rbgusrns/JP_Robotrace/Mechanics/STEP/SUCTION.STEP

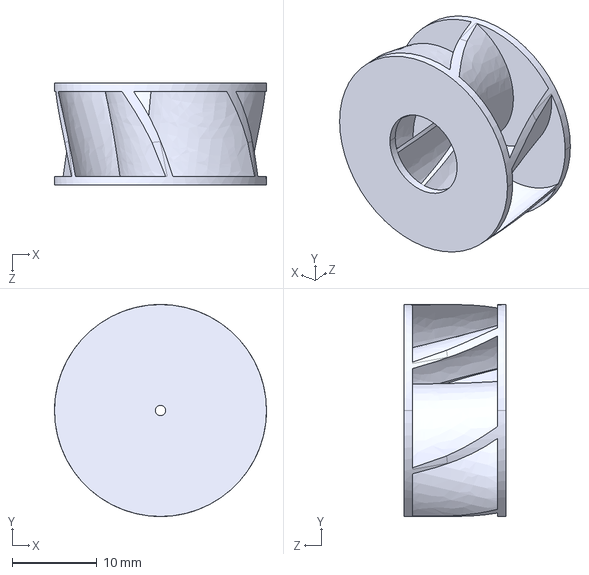
[picture p14: CAD file, 2026-03-30]
Mechanics/STEP/SUCTION.STEP
25.0 x 25.0 x 12.0 mm
