rbgusrns/JP_Robotrace/Software/main/fastrun.c

//###########################################################################
//
// FILE		: fastrun.c
//
// TITLE		: gungun_v2 Tracer fastrun source file.
//
// Author	: Park geon ju
//
// Company	: MAZE
//
//###########################################################################
// $Release Date: 2015.11.21 $
//###########################################################################


#include "DSP280x_Device.h"     // DSP280x Headerfile Include File
#include "DSP280x_Examples.h"   // DSP280x Examples Include File

static void turn_division_compute( fast_run_str *pinfo, int32 mark_cnt, error_str *perr ); 


// fast_error_compute( &g_err, pinfo, g_int32mark_cnt );	// 마크 에러처리  

void jerk_down( fast_run_str *pinfo, int32 mark_cnt )
{
	volatile _iq17 q17gone_dist = ( g_rm.q17gone_distance + g_lm.q17gone_distance ) >> 1;
	volatile _iq17 q17down_dist = _IQmpy(_IQ(pinfo->u16dist),_IQ(0.7));

	if( q17gone_dist > q17down_dist ) 
	{
		g_rm.int32accel = g_lm.int32accel = (int32)((g_q17user_acc>>17) + 2000 );
	}

}

void fast_error_compute( error_str *perr, fast_run_str *pinfo, int32 mark_cnt )
{
	fast_run_str *pnow;
	fast_run_str *pnext;

	volatile int32 dist = 0;
	volatile _iq17 big_vel = _IQ17(0.0);
	volatile _iq17 small_vel = _IQ17(0.0);

	perr->q17over_dist = ( g_rm.q17gone_distance + g_lm.q17gone_distance ) >> 1; // 현재 간 거리 계속 확인 	
	
	if( g_Flag.err )
	{
		g_Flag.fast_flag= OFF;
		return;
	}

	if( perr->q17over_dist > perr->q17err_dist[ mark_cnt ] ) // 마크에 주어진 에러값보다 더 간 경우 ( 마크를 놓친 경우) 
	{

		if(g_int32fasterror_flag)
		{
			if( g_int32err_cnt > 10 || mark_cnt > ( g_int32total_cnt - 1 ) ) // 1차 주행으로 전환 
			{
				VFDPrintf("   ERROR");

				g_Flag.err = ON;
				g_Flag.fast_flag= OFF;
			
				move_to_move(_IQ(1000), _IQ( 0 ), _IQ(1000) ,_IQ(1000), _IQ(5000));

				return;
			}
		}
		
		
		pnow = pinfo + mark_cnt;
		pnext = ( pinfo + mark_cnt + 1 );


		//	err_dst  - u16dist 
		dist = ( int32 )( (Uint16)(( perr->q17err_dist[ mark_cnt ] )>>17) - pnow->u16dist );

		pnext->u16dist -= dist;	// 실제 에러 수치를 다시 빼서 남은 거리를 구한다 . 
		if( pnext->u16dist <= 0 )
			pnext->u16dist = 10;

		//big_vel = ( pinfo->q17in_vel> pinfo->q17out_vel)? pinfo->q17in_vel : pinfo->q17out_vel;
		small_vel = ( pinfo->q17in_vel > pinfo->q17out_vel )? pinfo->q17out_vel : pinfo->q17in_vel;

		max_vel_compute( _IQ17( pnext->u16dist ), pnext->q17m_dist, small_vel, pnext->q17acc, &(pnext->q17vel) );	// 현재 거리와 등가속도에서 최고 속도를 계산 
		decel_dist_compute( pnext->q17vel, pnext->q17out_vel, pnext->q17acc, &(pnext->q17dec_dist) );			//  감속 거리 계산 

		perr->q17under_dist[ mark_cnt + 1 ] = _IQ17(( pnext->u16dist >> 1 ));

		second_infor( pinfo, perr);	// 마크를 강제로 처리한다.
		
	}

	
}


static void straight_compute( fast_run_str *pinfo, int32 mark_cnt, error_str *perr )  // straight, end compute
{ 
	volatile float32 big_vel = ( float32 )0.0;
	volatile float32 small_vel = ( float32 )0.0;


    
	pinfo->q17kp_val = POS_KP_UP;
	pinfo->s44s_flag = OFF;
	pinfo->speed_up_45 = OFF;

	//진입 속도, 탈출 속도 compute
	pinfo->q17in_vel = mark_cnt > 0 ? ( pinfo - 1 )->q17out_vel : _IQ17( 0.0);
    //첫 구간의 in_Vel = 0

	if( !( pinfo->u16turn_dir & ETURN ) )	//마지막 구간 아닐 경우. 일반적인 직진!
	{
		turn_division_compute( ( pinfo + 1 ), ( mark_cnt + 1 ), perr );	//다음 턴 미리 계산한 후에 out vel 결정
		pinfo->q17out_vel = ( pinfo + 1 )->q17in_vel;

		pinfo->q17out_vel = g_q17user_vel;			//턴속 모든 각에서 동일하게 맞춤 
	}
	else	//마지막 구간. ETURN
		( pinfo + 1 )->q17in_vel = pinfo->q17out_vel = g_q17end_vel;
		//( pinfo + 1 )->q17in_vel = pinfo->q17out_vel = _IQ17( 0.0);
		// 엔드마크의 in_Vel = 마지막 구간의 out_Vel = end_Vel
	//직진 길이별 가속도 설정
	
	if( pinfo->u16dist > LONG_DIST )        pinfo->q17acc = g_q17user_acc;
	else if( pinfo->u16dist> MID_DIST )		pinfo->q17acc = g_q17user_acc; //+ _IQ17(1000);  // 중간 직진 가속 
	else									pinfo->q17acc = g_q17user_acc;// + _IQ17(4000);

    if( pinfo->u16turn_dir & ETURN )        pinfo->q17acc = g_q17endturn_acc;

	if( !mark_cnt && pinfo->q17acc > _IQ17(10000) )	pinfo->q17acc = _IQ17(10000); // 시작 직전 가속도 제한

	big_vel = ( pinfo->q17in_vel> pinfo->q17out_vel)? pinfo->q17in_vel : pinfo->q17out_vel;
	small_vel = ( pinfo->q17in_vel > pinfo->q17out_vel )? pinfo->q17out_vel : pinfo->q17in_vel;
	
	decel_dist_compute( pinfo->q17in_vel, pinfo->q17out_vel, pinfo->q17acc, &pinfo->q17m_dist); // pinfo->q17m_dist 구함 
    //진입속도와 탈출속도, 가속도를 통해 감속 거리를 구함.
	if( pinfo->q17m_dist >=  _IQ17( ( pinfo->u16dist) ) ) // start or end
	{
		pinfo->q17dec_dist = _IQ17( ( pinfo->u16dist) );


		max_vel_compute( _IQ17( pinfo->u16dist ), _IQ17(0.0), small_vel, pinfo->q17acc , &pinfo->q17vel ); //pinfo->q17vel 구함 
		
		if( pinfo->q17in_vel > pinfo->q17out_vel )		pinfo->q17in_vel = pinfo->q17vel; // end
		else											pinfo->q17out_vel = pinfo->q17vel; // start 

		if( !mark_cnt )		//시작 직진
			pinfo->q17in_vel = _IQ17(0.0);
	}
	else
	{	
		max_vel_compute( _IQ17( pinfo->u16dist ), pinfo->q17m_dist, big_vel, pinfo->q17acc, &pinfo->q17vel );
		decel_dist_compute( pinfo->q17vel, pinfo->q17out_vel, pinfo->q17acc, &pinfo->q17dec_dist );
	}

	//에러 처리
	perr->q17err_dist[ mark_cnt ] = _IQ17( pinfo->u16dist << 2 );

	if( perr->q17err_dist[ mark_cnt ] > _IQ17( MID_DIST + SHORT_DIST ) )
		perr->q17err_dist[ mark_cnt ] = _IQ17( MID_DIST + SHORT_DIST );

	perr->q17err_dist[ mark_cnt ] += _IQ17( pinfo->u16dist );  // 곡률마다 에러값 지정. 마크를 못봤을 떄 필요 
	perr->q17under_dist[ mark_cnt ] = _IQmpy(_IQ17( pinfo->u16dist ) , _IQ17(0.9)); // 마크를 더 봤을 때 필요 

}


static void default_turn_compute( fast_run_str *pinfo, int32 mark_cnt, error_str *perr )
{
	pinfo->q17kp_val = POS_KP_UP;
	pinfo->s44s_flag = OFF;
	pinfo->speed_up_45 = OFF;

	pinfo->q17acc = g_q17user_acc;

	pinfo->q17in_vel = g_q17user_vel;
	pinfo->q17vel = pinfo->q17out_vel = pinfo->q17in_vel;

	//에러처리
	perr->q17err_dist[ mark_cnt ] = _IQmpy(_IQ17( pinfo->u16dist) ,_IQ17(0.5));
	perr->q17err_dist[ mark_cnt ] += _IQ17( pinfo->u16dist );

	perr->q17under_dist[ mark_cnt ] = _IQmpy(_IQ17( pinfo->u16dist) ,_IQ17(0.9));
	
	//45도 연속 

	if( ( pinfo->u16turn_dir & TURN_45 ) && ( ( pinfo + 1 )->u16turn_dir & ( TURN_45 | TURN_90 ) ) )
	{
		pinfo->speed_up_45 = ON;
		pinfo->q17kp_val = _IQ7(0.15);
		
		//에러처리
		perr->q17err_dist[ mark_cnt ] = _IQ17( pinfo->u16dist << 2 );
		perr->q17under_dist[ mark_cnt ] =_IQmpy(_IQ17( pinfo->u16dist) ,_IQ17(0.9));

        
	}


}

void large_turn_compute( fast_run_str *pinfo, int32 mark_cnt, error_str *perr )
{
	volatile _iq17 big_vel = _IQ17(0.0);
	volatile _iq17 small_vel = _IQ17(0.0);

	pinfo->q17kp_val = POS_KP_UP;
	pinfo->s44s_flag = OFF;
	pinfo->speed_up_45 = OFF;

	pinfo->q17in_vel = ( pinfo - 1 )->q17out_vel ? ( pinfo - 1 )->q17out_vel : g_q17user_vel;
	
	turn_division_compute( ( pinfo + 1 ), ( mark_cnt + 1 ), perr ); // 다음 턴 미리 계산한 후에 out_vel 결정 
	pinfo->q17out_vel = ( pinfo + 1 )->q17in_vel;

	

	if( pinfo->q17out_vel == _IQ17(0.0))				pinfo->q17out_vel = ( g_q17user_vel);
	if( pinfo->q17in_vel > ( g_q17large_vel) )			pinfo->q17in_vel = ( g_q17large_vel );
	if( pinfo->q17out_vel > ( g_q17large_vel ) )		pinfo->q17out_vel = ( g_q17large_vel );
	pinfo->q17acc = g_q17large_acc;


	big_vel = ( pinfo->q17in_vel> pinfo->q17out_vel)? pinfo->q17in_vel : pinfo->q17out_vel;
	small_vel = ( pinfo->q17in_vel > pinfo->q17out_vel )? pinfo->q17out_vel : pinfo->q17in_vel;
	decel_dist_compute( pinfo->q17in_vel, pinfo->q17out_vel, pinfo->q17acc, &pinfo->q17m_dist );

	if( pinfo->q17m_dist >=  _IQ17( ( pinfo->u16dist) ) )
	{
		pinfo->q17dec_dist = _IQ17( ( pinfo->u16dist) );
		max_vel_compute( _IQ17( pinfo->u16dist ), _IQ17(0.0), small_vel, pinfo->q17acc , &pinfo->q17vel );

		if( pinfo->q17in_vel > pinfo->q17out_vel )		pinfo->q17in_vel = pinfo->q17vel;
		else											pinfo->q17out_vel = pinfo->q17vel;

		if( !mark_cnt )		//시작 직진
			pinfo->q17in_vel = _IQ17(0.0);
	}
	else
	{
		
		
		max_vel_compute( _IQ17( pinfo->u16dist ), pinfo->q17m_dist, big_vel, pinfo->q17acc, &pinfo->q17vel );
		decel_dist_compute( pinfo->q17vel, pinfo->q17out_vel, pinfo->q17acc, &pinfo->q17dec_dist );

		//if( ((pinfo + 1)->u16turn_way & STRAIGHT) && ( (pinfo + 1)->u16dist > SHORT_DIST) ) ( pinfo + 1 )->q17in_vel = pinfo->q17out_vel = pinfo->q17vel;		// 다음턴이 직진인 경우 q17vel로 탈출  // 큰턴 + 직진 가속 
	}


	//에러 처리
	perr->q17err_dist[ mark_cnt ] = _IQ17( pinfo->u16dist << 2 );
	if( perr->q17err_dist[ mark_cnt ] > _IQ17( MID_DIST + SHORT_DIST ) )
		perr->q17err_dist[ mark_cnt ] = _IQ17( MID_DIST + SHORT_DIST );

	perr->q17err_dist[ mark_cnt ] += _IQ17( pinfo->u16dist );
	perr->q17under_dist[ mark_cnt ] = _IQmpy(_IQ17( pinfo->u16dist ) , _IQ17(0.9));

}


static void turn_division_compute( fast_run_str *pinfo, int32 mark_cnt, error_str *perr ) // 직진, 큰턴, 턴 구분 
{
    TxPrintf("way: %d\n",pinfo->u16turn_dir);
	if( pinfo->u16turn_way & (STRAIGHT | ETURN ) )			                            straight_compute( pinfo, mark_cnt, perr );
	else if( pinfo->u16turn_dir & LARGE_TURN )											default_turn_compute( pinfo, mark_cnt, perr ); //large_turn_compute( pinfo, mark_cnt, perr );
	else																				default_turn_compute( pinfo, mark_cnt, perr );
}

void turn_division_func( void )
{
		int32 i = 0;
		TxPrintf("cnt: %ld\n",g_int32total_cnt);
		for( i = 0; i < g_int32total_cnt; i++ )
		{
			/*
			if( 1 == ( g_int32total_cnt - 1 ) )
			{
				if( g_fast_info[ i ].q17acc>= _IQ17(12000) )
					g_fast_info[ i ].q17acc = _IQ17(12000);
					g_q17end_acc = g_fast_info[ i ].q17acc;

			}
			*/

			turn_division_compute( &g_fast_info[ i ], i, &g_err );

			
		}
	
	
}


void speed_up_compute( fast_run_str *p_info )
{
	fast_run_str *pinfo = p_info;

	
	if( !g_Flag.speed_up_start || g_Flag.err )	return;
#if 0
	g_int32speed_up_cnt ++;
	if( g_int32speed_up_cnt > ( pinfo + g_int32mark_cnt - 1 )->u16turn_cnt  || !( g_int32mark_cnt ) )
	{
        
		g_Flag.speed_up = ON;
		g_Flag.speed_up_start = OFF;
		g_int32speed_up_cnt = 0;
	}
#endif

#if 1
	if( g_q17straight_dist >= ( _IQ(( pinfo + g_int32mark_cnt - 1 )->u16turn_cnt) )  || !( g_int32mark_cnt ) )
	{
		g_Flag.speed_up = ON;
		g_Flag.speed_up_start = OFF;
		g_int32speed_up_cnt = 0;
	}
#endif


}


void second_infor(fast_run_str * p_info, error_str *perr )
{

	fast_run_str *pinfo = p_info;

	// 턴마크 나올 거리가 안됐을 경우(마크를 더 찍은 경우) 
	if( g_Flag.err || ( perr->q17over_dist < perr->q17under_dist[ g_int32mark_cnt ] ) )	
    {
        return;
    }
    
    //if( ( ( pinfo + g_int32mark_cnt + 1 )->u16turn_dir & ( STRAIGHT | ETURN ) ) && !( g_pos.u16current_state & STRAIGHT ) )
    //{
    //    return;
    //}    

    //if( !( ( pinfo + g_int32mark_cnt + 1 )->u16turn_way & g_pos.u16current_state ) )
    //{
    //    return;
    //}
	g_int32mark_cnt ++; // 저장된 곡률보다 한칸 뒷 정보를 불러와야 함. 


	if( g_Flag.err == OFF )
	{

		if( ( g_int32total_cnt + 5 ) < g_int32mark_cnt )
		{
			g_Flag.err = ON;
			g_lm.q17gone_distance = g_rm.q17gone_distance = _IQ17(0.0); // 검출용 변수들 다시 초기화 
			return;
		}
	}

	if( ( pinfo + g_int32mark_cnt )->u16turn_dir & ( STRAIGHT | LARGE_TURN | ETURN ) )
    {
            g_Flag.speed_up_start = ON;  // 가속 시작 flag on
            g_lmark.u16mark_enable = FRONT_MARK_CHECK;
            
	}
    else if( ( pinfo + g_int32mark_cnt )->q17kp_val == POS_KP_DOWN )
    {
            g_lmark.u16mark_enable = ( FRONT_MARK_CHECK | LEFT_MARK_CHECK );
    }
	else																					
    {
        g_Flag.straight_run = OFF;
        g_lmark.u16mark_enable = LEFT_MARK_CHECK;
	}


	move_to_move( _IQ17( ( pinfo + g_int32mark_cnt )->u16dist ), ( pinfo + g_int32mark_cnt )->q17dec_dist, ( pinfo + g_int32mark_cnt )->q17vel, ( pinfo + g_int32mark_cnt )->q17out_vel, ( pinfo + g_int32mark_cnt )->q17acc );
    
	perr->q17over_dist = _IQ17( 0.0 );
	g_lm.q17gone_distance = g_rm.q17gone_distance = _IQ17(0.0); // 검출용 변수들 다시 초기화 
	g_lm.q17total_dist = g_rm.q17total_dist = _IQ(0.0);
    g_rm.q17dist_sum = g_lm.q17dist_sum = _IQ(0.0);
 
	g_pos.u16past_state = ( pinfo + g_int32mark_cnt )->u16turn_dir;	
    
}

   
void print_sec_info(fast_run_str *pinfo)
{
	race_start_init();
	//fast_infor_read_rom(); 
	turn_info_func();
	turn_division_func();

	//g_fast_info[g_int32total_cnt-1].q17out_vel = _IQ(2400);	// 마지막 탈출속도 고정
	print_second_info();
}

void second_run(fast_run_str *pinfo)
{	
	
	//int32 i = 0;
	
	race_start_init();
	//fast_infor_read_rom(); 
	turn_info_func();
	turn_division_func();
    //print_second_info();
	
	VFDPrintf("fst %f",_IQ17toF(g_q17user_vel));	

    DELAY_US(500000);

    FAN_ON;
    
	DELAY_US(1000000);
    
	VFDPrintf("        ");

	
	// 1차 handle : 0.52 1.88 / 
	handle_ad_make(g_q16out_corner_fast_limit, g_q16in_corner_fast_limit); // _IQ16(0.35) , _IQ16(2.05);
	move_to_move( _IQ17( pinfo->u16dist ), pinfo->q17dec_dist, pinfo->q17vel, pinfo->q17out_vel, pinfo->q17acc );
    //TxPrintf("%d,%ld,%ld,%ld,%ld\n",pinfo->u16dist, pinfo->q17dec_dist >> 17 , pinfo->q17vel >> 17 , pinfo->q17out_vel >> 17 , pinfo->q17acc >> 17 );
	g_Flag.fast_flag = ON;
	g_Flag.motor_start = ON;
	
	while(1)
	{
        //TxPrintf("%f,%f,%f,%f,%ld,%d,%d,%ld\n",_IQtoF(g_q17current_omega),_IQtoF(g_err.q17err_dist[ g_int32mark_cnt ]),_IQtoF(g_err.q17under_dist[ g_int32mark_cnt ]),_IQtoF(g_err.q17over_dist),g_int32mark_cnt,g_pos.u16past_state<<6,g_pos.u16current_state<<6,g_int32err_cnt );
         //TxPrintf("%f,%ld\n",_IQtoF(g_q17current_omega),g_int32mark_cnt);
        //TxPrintf("%f,%f,%ld,%u,%u\n",_IQtoF(g_q17current_omega),_IQtoF(g_err.q17over_dist),g_int32mark_cnt,g_pos.u16current_state<<6,(pinfo+g_int32mark_cnt)->u16turn_way<<6);
        //LED_ON;
        g_q17straight_dist = (g_rm.q17gone_distance + g_lm.q17gone_distance) >> 1 ;
	
		make_position();
		
		if(g_Flag.move_state)
		{
			g_lmark.q7turn_dis = (g_lmark.q7check_dis + g_rmark.q7check_dis) >> 1;
			g_rmark.q7turn_dis = g_lmark.q7turn_dis;
	
			turn_decide( g_ptr->g_lmark );
			turn_decide( g_ptr->g_rmark );
			
			
		}

						
		if( g_Flag.motor_ISR_flag )
		{
			if( lineout_func())
			{
                g_Flag.motor_ISR_flag = OFF;
				return;
			}

			speed_up_compute( pinfo );
            fast_error_compute( &g_err, pinfo, g_int32mark_cnt );		        
			g_Flag.motor_ISR_flag = OFF;
		}	
        //LED_OFF;
	}
}
