rbgusrns/JP_Robotrace/Software/include/IQmathLib.h

//###########################################################################
//
// FILE:	IQmathLib.h
//
// TITLE:	IQ Math library functions definitions.
//
//###########################################################################
//
// Ver  | dd-mmm-yyyy |  Who  | Description of changes
// =====|=============|=======|==============================================
//  1.3 | 19 Nov 2001 | A. T. | Original Release.
// -----|-------------|-------|----------------------------------------------
//  1.4 | 17 May 2002 | A. T. | Added new functions and support for
//      |             |       | intrinsics IQmpy, IQxmpy, IQsat.
// -----|-------------|-------|----------------------------------------------
//  1.4a| 12 Jun 2002 | A. T. | Fixed problem with _IQ() operation on
//      |             |       | variables.
// -----|-------------|-------|----------------------------------------------
//  1.4b| 18 Jun 2002 | A. T. | Fixed bug with _IQtoIQN() and _IQNtoIQ()
//      |             |       | operations.
// -----|-------------|-------|----------------------------------------------
//  1.4d| 30 Mar 2003 | DA/SD | 1. Added macro parameters in parentheses 
//      |             |       |    in number of places where it matters
//      |             |       | 2. Added macro definition to include header 
//      |             |       |    file multiple times in the program.     
// -----|-------------|-------|----------------------------------------------
//
//###########################################################################
// 
// User needs to configure "MATH_TYPE" and "GLOBAL_Q" values:
//
//---------------------------------------------------------------------------
// Select math type, IQ_MATH or FLOAT_MATH:
//

#ifndef __IQMATHLIB_H_INCLUDED__
#define __IQMATHLIB_H_INCLUDED__


#define   FLOAT_MATH     1
#define   IQ_MATH        0

#ifndef   MATH_TYPE
#define   MATH_TYPE      IQ_MATH
#endif

//---------------------------------------------------------------------------
// Select global Q value and scaling. The Q value is limited to the 
// following range for all functions:
//
//        30 <= GLOBAL_Q <=  1
//
#ifndef   GLOBAL_Q
#define   GLOBAL_Q       17
#endif

//---------------------------------------------------------------------------
// Various Usefull Constant Definitions:
//
#define   QG          GLOBAL_Q
#define   Q30         30
#define   Q29         29
#define   Q28         28
#define   Q27         27
#define   Q26         26
#define   Q25         25
#define   Q24         24
#define   Q23         23
#define   Q22         22
#define   Q21         21
#define   Q20         20
#define   Q19         19
#define   Q18         18
#define   Q17         17
#define   Q16         16
#define   Q15         15
#define   Q14         14
#define   Q13         13
#define   Q12         12
#define   Q11         11
#define   Q10         10
#define   Q9          9
#define   Q8          8
#define   Q7          7
#define   Q6          6
#define   Q5          5
#define   Q4          4
#define   Q3          3
#define   Q2          2
#define   Q1          1

#define   MAX_IQ_POS  2147483647 
#define   MAX_IQ_NEG  -2147483648
#define   MIN_IQ_POS  1
#define   MIN_IQ_NEG  -1

//###########################################################################
#if MATH_TYPE == IQ_MATH
//###########################################################################
// If IQ_MATH is used, the following IQmath library function definitions
// are used:
//===========================================================================
typedef   long    _iq;
typedef   long    _iq30;
typedef   long    _iq29;
typedef   long    _iq28;
typedef   long    _iq27;
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

#define   _IQtoIQ28(A)  ((GLOBAL_Q >= 28) ? ((long) (A) >> (GLOBAL_Q - 28)):((long) (A) << (28 - GLOBAL_Q)))
#define   _IQ28toIQ(A)  ((GLOBAL_Q >= 28) ? ((long) (A) << (GLOBAL_Q - 28)):((long) (A) >> (28 - GLOBAL_Q)))

#define   _IQtoIQ27(A)  ((GLOBAL_Q >= 27) ? ((long) (A) >> (GLOBAL_Q - 27)):((long) (A) << (27 - GLOBAL_Q)))
#define   _IQ27toIQ(A)  ((GLOBAL_Q >= 27) ? ((long) (A) << (GLOBAL_Q - 27)):((long) (A) >> (27 - GLOBAL_Q)))

#define   _IQtoIQ26(A)  ((GLOBAL_Q >= 26) ? ((long) (A) >> (GLOBAL_Q - 26)):((long) (A) << (26 - GLOBAL_Q)))
#define   _IQ26toIQ(A)  ((GLOBAL_Q >= 26) ? ((long) (A) << (GLOBAL_Q - 26)):((long) (A) >> (26 - GLOBAL_Q)))

#define   _IQtoIQ25(A)  ((GLOBAL_Q >= 25) ? ((long) (A) >> (GLOBAL_Q - 25)):((long) (A) << (25 - GLOBAL_Q)))
#define   _IQ25toIQ(A)  ((GLOBAL_Q >= 25) ? ((long) (A) << (GLOBAL_Q - 25)):((long) (A) >> (25 - GLOBAL_Q)))

#define   _IQtoIQ24(A)  ((GLOBAL_Q >= 24) ? ((long) (A) >> (GLOBAL_Q - 24)):((long) (A) << (24 - GLOBAL_Q)))
#define   _IQ24toIQ(A)  ((GLOBAL_Q >= 24) ? ((long) (A) << (GLOBAL_Q - 24)):((long) (A) >> (24 - GLOBAL_Q)))

#define   _IQtoIQ23(A)  ((GLOBAL_Q >= 23) ? ((long) (A) >> (GLOBAL_Q - 23)):((long) (A) << (23 - GLOBAL_Q)))
#define   _IQ23toIQ(A)  ((GLOBAL_Q >= 23) ? ((long) (A) << (GLOBAL_Q - 23)):((long) (A) >> (23 - GLOBAL_Q)))

#define   _IQtoIQ22(A)  ((GLOBAL_Q >= 22) ? ((long) (A) >> (GLOBAL_Q - 22)):((long) (A) << (22 - GLOBAL_Q)))
#define   _IQ22toIQ(A)  ((GLOBAL_Q >= 22) ? ((long) (A) << (GLOBAL_Q - 22)):((long) (A) >> (22 - GLOBAL_Q)))

#define   _IQtoIQ21(A)  ((GLOBAL_Q >= 21) ? ((long) (A) >> (GLOBAL_Q - 21)):((long) (A) << (21 - GLOBAL_Q)))
#define   _IQ21toIQ(A)  ((GLOBAL_Q >= 21) ? ((long) (A) << (GLOBAL_Q - 21)):((long) (A) >> (21 - GLOBAL_Q)))

#define   _IQtoIQ20(A)  ((GLOBAL_Q >= 20) ? ((long) (A) >> (GLOBAL_Q - 20)):((long) (A) << (20 - GLOBAL_Q)))
#define   _IQ20toIQ(A)  ((GLOBAL_Q >= 20) ? ((long) (A) << (GLOBAL_Q - 20)):((long) (A) >> (20 - GLOBAL_Q)))

#define   _IQtoIQ19(A)  ((GLOBAL_Q >= 19) ? ((long) (A) >> (GLOBAL_Q - 19)):((long) (A) << (19 - GLOBAL_Q)))
#define   _IQ19toIQ(A)  ((GLOBAL_Q >= 19) ? ((long) (A) << (GLOBAL_Q - 19)):((long) (A) >> (19 - GLOBAL_Q)))

#define   _IQtoIQ18(A)  ((GLOBAL_Q >= 18) ? ((long) (A) >> (GLOBAL_Q - 18)):((long) (A) << (18 - GLOBAL_Q)))
#define   _IQ18toIQ(A)  ((GLOBAL_Q >= 18) ? ((long) (A) << (GLOBAL_Q - 18)):((long) (A) >> (18 - GLOBAL_Q)))

#define   _IQtoIQ17(A)  ((GLOBAL_Q >= 17) ? ((long) (A) >> (GLOBAL_Q - 17)):((long) (A) << (17 - GLOBAL_Q)))
#define   _IQ17toIQ(A)  ((GLOBAL_Q >= 17) ? ((long) (A) << (GLOBAL_Q - 17)):((long) (A) >> (17 - GLOBAL_Q)))

#define   _IQtoIQ16(A)  ((GLOBAL_Q >= 16) ? ((long) (A) >> (GLOBAL_Q - 16)):((long) (A) << (16 - GLOBAL_Q)))
#define   _IQ16toIQ(A)  ((GLOBAL_Q >= 16) ? ((long) (A) << (GLOBAL_Q - 16)):((long) (A) >> (16 - GLOBAL_Q)))

#define   _IQtoIQ15(A)  ((GLOBAL_Q >= 15) ? ((long) (A) >> (GLOBAL_Q - 15)):((long) (A) << (15 - GLOBAL_Q)))
#define   _IQ15toIQ(A)  ((GLOBAL_Q >= 15) ? ((long) (A) << (GLOBAL_Q - 15)):((long) (A) >> (15 - GLOBAL_Q)))

#define   _IQtoIQ14(A)  ((GLOBAL_Q >= 14) ? ((long) (A) >> (GLOBAL_Q - 14)):((long) (A) << (14 - GLOBAL_Q)))
#define   _IQ14toIQ(A)  ((GLOBAL_Q >= 14) ? ((long) (A) << (GLOBAL_Q - 14)):((long) (A) >> (14 - GLOBAL_Q)))

#define   _IQtoIQ13(A)  ((GLOBAL_Q >= 13) ? ((long) (A) >> (GLOBAL_Q - 13)):((long) (A) << (13 - GLOBAL_Q)))
#define   _IQ13toIQ(A)  ((GLOBAL_Q >= 13) ? ((long) (A) << (GLOBAL_Q - 13)):((long) (A) >> (13 - GLOBAL_Q)))

#define   _IQtoIQ12(A)  ((GLOBAL_Q >= 12) ? ((long) (A) >> (GLOBAL_Q - 12)):((long) (A) << (12 - GLOBAL_Q)))
#define   _IQ12toIQ(A)  ((GLOBAL_Q >= 12) ? ((long) (A) << (GLOBAL_Q - 12)):((long) (A) >> (12 - GLOBAL_Q)))

#define   _IQtoIQ11(A)  ((GLOBAL_Q >= 11) ? ((long) (A) >> (GLOBAL_Q - 11)):((long) (A) << (11 - GLOBAL_Q)))
#define   _IQ11toIQ(A)  ((GLOBAL_Q >= 11) ? ((long) (A) << (GLOBAL_Q - 11)):((long) (A) >> (11 - GLOBAL_Q)))

#define   _IQtoIQ10(A)  ((GLOBAL_Q >= 10) ? ((long) (A) >> (GLOBAL_Q - 10)):((long) (A) << (10 - GLOBAL_Q)))
#define   _IQ10toIQ(A)  ((GLOBAL_Q >= 10) ? ((long) (A) << (GLOBAL_Q - 10)):((long) (A) >> (10 - GLOBAL_Q)))

#define   _IQtoIQ9(A)   ((GLOBAL_Q >= 9) ? ((long) (A) >> (GLOBAL_Q - 9)):((long) (A) << (9 - GLOBAL_Q)))
#define   _IQ9toIQ(A)   ((GLOBAL_Q >= 9) ? ((long) (A) << (GLOBAL_Q - 9)):((long) (A) >> (9 - GLOBAL_Q)))

#define   _IQtoIQ8(A)   ((GLOBAL_Q >= 8) ? ((long) (A) >> (GLOBAL_Q - 8)):((long) (A) << (8 - GLOBAL_Q)))
#define   _IQ8toIQ(A)   ((GLOBAL_Q >= 8) ? ((long) (A) << (GLOBAL_Q - 8)):((long) (A) >> (8 - GLOBAL_Q)))

#define   _IQtoIQ7(A)   ((GLOBAL_Q >= 7) ? ((long) (A) >> (GLOBAL_Q - 7)):((long) (A) << (7 - GLOBAL_Q)))
#define   _IQ7toIQ(A)   ((GLOBAL_Q >= 7) ? ((long) (A) << (GLOBAL_Q - 7)):((long) (A) >> (7 - GLOBAL_Q)))

#define   _IQtoIQ6(A)   ((GLOBAL_Q >= 6) ? ((long) (A) >> (GLOBAL_Q - 6)):((long) (A) << (6 - GLOBAL_Q)))
#define   _IQ6toIQ(A)   ((GLOBAL_Q >= 6) ? ((long) (A) << (GLOBAL_Q - 6)):((long) (A) >> (6 - GLOBAL_Q)))

#define   _IQtoIQ5(A)   ((GLOBAL_Q >= 5) ? ((long) (A) >> (GLOBAL_Q - 5)):((long) (A) << (5 - GLOBAL_Q)))
#define   _IQ5toIQ(A)   ((GLOBAL_Q >= 5) ? ((long) (A) << (GLOBAL_Q - 5)):((long) (A) >> (5 - GLOBAL_Q)))

#define   _IQtoIQ4(A)   ((GLOBAL_Q >= 4) ? ((long) (A) >> (GLOBAL_Q - 4)):((long) (A) << (4 - GLOBAL_Q)))
#define   _IQ4toIQ(A)   ((GLOBAL_Q >= 4) ? ((long) (A) << (GLOBAL_Q - 4)):((long) (A) >> (4 - GLOBAL_Q)))

#define   _IQtoIQ3(A)   ((GLOBAL_Q >= 3) ? ((long) (A) >> (GLOBAL_Q - 3)):((long) (A) << (3 - GLOBAL_Q)))
#define   _IQ3toIQ(A)   ((GLOBAL_Q >= 3) ? ((long) (A) << (GLOBAL_Q - 3)):((long) (A) >> (3 - GLOBAL_Q)))

#define   _IQtoIQ2(A)   ((GLOBAL_Q >= 2) ? ((long) (A) >> (GLOBAL_Q - 2)):((long) (A) << (2 - GLOBAL_Q)))
#define   _IQ2toIQ(A)   ((GLOBAL_Q >= 2) ? ((long) (A) << (GLOBAL_Q - 2)):((long) (A) >> (2 - GLOBAL_Q)))

#define   _IQtoIQ1(A)   ((long) (A) >> (GLOBAL_Q - 1))
#define   _IQ1toIQ(A)   ((long) (A) << (GLOBAL_Q - 1))
//---------------------------------------------------------------------------
#define   _IQtoQ15(A)   ((GLOBAL_Q >= 15) ? ((long) (A) >> (GLOBAL_Q - 15)):((long) (A) << (15 - GLOBAL_Q)))
#define   _Q15toIQ(A)   ((GLOBAL_Q >= 15) ? ((long) (A) << (GLOBAL_Q - 15)):((long) (A) >> (15 - GLOBAL_Q)))

#define   _IQtoQ14(A)   ((GLOBAL_Q >= 14) ? ((long) (A) >> (GLOBAL_Q - 14)):((long) (A) << (14 - GLOBAL_Q)))
#define   _Q14toIQ(A)   ((GLOBAL_Q >= 14) ? ((long) (A) << (GLOBAL_Q - 14)):((long) (A) >> (14 - GLOBAL_Q)))

#define   _IQtoQ13(A)   ((GLOBAL_Q >= 13) ? ((long) (A) >> (GLOBAL_Q - 13)):((long) (A) << (13 - GLOBAL_Q)))
#define   _Q13toIQ(A)   ((GLOBAL_Q >= 13) ? ((long) (A) << (GLOBAL_Q - 13)):((long) (A) >> (13 - GLOBAL_Q)))

#define   _IQtoQ12(A)   ((GLOBAL_Q >= 12) ? ((long) (A) >> (GLOBAL_Q - 12)):((long) (A) << (12 - GLOBAL_Q)))
#define   _Q12toIQ(A)   ((GLOBAL_Q >= 12) ? ((long) (A) << (GLOBAL_Q - 12)):((long) (A) >> (12 - GLOBAL_Q)))

#define   _IQtoQ11(A)   ((GLOBAL_Q >= 11) ? ((long) (A) >> (GLOBAL_Q - 11)):((long) (A) << (11 - GLOBAL_Q)))
#define   _Q11toIQ(A)   ((GLOBAL_Q >= 11) ? ((long) (A) << (GLOBAL_Q - 11)):((long) (A) >> (11 - GLOBAL_Q)))

#define   _IQtoQ10(A)   ((GLOBAL_Q >= 10) ? ((long) (A) >> (GLOBAL_Q - 10)):((long) (A) << (10 - GLOBAL_Q)))
#define   _Q10toIQ(A)   ((GLOBAL_Q >= 10) ? ((long) (A) << (GLOBAL_Q - 10)):((long) (A) >> (10 - GLOBAL_Q)))

#define   _IQtoQ9(A)    ((GLOBAL_Q >= 9) ? ((long) (A) >> (GLOBAL_Q - 9)):((long) (A) << (9 - GLOBAL_Q)))
#define   _Q9toIQ(A)    ((GLOBAL_Q >= 9) ? ((long) (A) << (GLOBAL_Q - 9)):((long) (A) >> (9 - GLOBAL_Q)))

#define   _IQtoQ8(A)    ((GLOBAL_Q >= 8) ? ((long) (A) >> (GLOBAL_Q - 8)):((long) (A) << (8 - GLOBAL_Q)))
#define   _Q8toIQ(A)    ((GLOBAL_Q >= 8) ? ((long) (A) << (GLOBAL_Q - 8)):((long) (A) >> (8 - GLOBAL_Q)))

#define   _IQtoQ7(A)    ((GLOBAL_Q >= 7) ? ((long) (A) >> (GLOBAL_Q - 7)):((long) (A) << (7 - GLOBAL_Q)))
#define   _Q7toIQ(A)    ((GLOBAL_Q >= 7) ? ((long) (A) << (GLOBAL_Q - 7)):((long) (A) >> (7 - GLOBAL_Q)))

#define   _IQtoQ6(A)    ((GLOBAL_Q >= 6) ? ((long) (A) >> (GLOBAL_Q - 6)):((long) (A) << (6 - GLOBAL_Q)))
#define   _Q6toIQ(A)    ((GLOBAL_Q >= 6) ? ((long) (A) << (GLOBAL_Q - 6)):((long) (A) >> (6 - GLOBAL_Q)))

#define   _IQtoQ5(A)    ((GLOBAL_Q >= 5) ? ((long) (A) >> (GLOBAL_Q - 5)):((long) (A) << (5 - GLOBAL_Q)))
#define   _Q5toIQ(A)    ((GLOBAL_Q >= 5) ? ((long) (A) << (GLOBAL_Q - 5)):((long) (A) >> (5 - GLOBAL_Q)))

#define   _IQtoQ5(A)    ((GLOBAL_Q >= 5) ? ((long) (A) >> (GLOBAL_Q - 5)):((long) (A) << (5 - GLOBAL_Q)))
#define   _Q5toIQ(A)    ((GLOBAL_Q >= 5) ? ((long) (A) << (GLOBAL_Q - 5)):((long) (A) >> (5 - GLOBAL_Q)))

#define   _IQtoQ4(A)    ((GLOBAL_Q >= 4) ? ((long) (A) >> (GLOBAL_Q - 4)):((long) (A) << (4 - GLOBAL_Q)))
#define   _Q4toIQ(A)    ((GLOBAL_Q >= 4) ? ((long) (A) << (GLOBAL_Q - 4)):((long) (A) >> (4 - GLOBAL_Q)))

#define   _IQtoQ3(A)    ((GLOBAL_Q >= 3) ? ((long) (A) >> (GLOBAL_Q - 3)):((long) (A) << (3 - GLOBAL_Q)))
#define   _Q3toIQ(A)    ((GLOBAL_Q >= 3) ? ((long) (A) << (GLOBAL_Q - 3)):((long) (A) >> (3 - GLOBAL_Q)))

#define   _IQtoQ2(A)    ((GLOBAL_Q >= 2) ? ((long) (A) >> (GLOBAL_Q - 2)):((long) (A) << (2 - GLOBAL_Q)))
#define   _Q2toIQ(A)    ((GLOBAL_Q >= 2) ? ((long) (A) << (GLOBAL_Q - 2)):((long) (A) >> (2 - GLOBAL_Q)))

#define   _IQtoQ1(A)    ((GLOBAL_Q >= 1) ? ((long) (A) >> (GLOBAL_Q - 1)):((long) (A) << (1 - GLOBAL_Q)))
#define   _Q1toIQ(A)    ((GLOBAL_Q >= 1) ? ((long) (A) << (GLOBAL_Q - 1)):((long) (A) >> (1 - GLOBAL_Q)))
//---------------------------------------------------------------------------
#define   _IQmpy(A,B)    __IQmpy(A,B,GLOBAL_Q)
#define   _IQ30mpy(A,B)  __IQmpy(A,B,30)
#define   _IQ29mpy(A,B)  __IQmpy(A,B,29)
#define   _IQ28mpy(A,B)  __IQmpy(A,B,28)
#define   _IQ27mpy(A,B)  __IQmpy(A,B,27)
#define   _IQ26mpy(A,B)  __IQmpy(A,B,26)
#define   _IQ25mpy(A,B)  __IQmpy(A,B,25)
#define   _IQ24mpy(A,B)  __IQmpy(A,B,24)
#define   _IQ23mpy(A,B)  __IQmpy(A,B,23)
#define   _IQ22mpy(A,B)  __IQmpy(A,B,22)
#define   _IQ21mpy(A,B)  __IQmpy(A,B,21)
#define   _IQ20mpy(A,B)  __IQmpy(A,B,20)
#define   _IQ19mpy(A,B)  __IQmpy(A,B,19)
#define   _IQ18mpy(A,B)  __IQmpy(A,B,18)
#define   _IQ17mpy(A,B)  __IQmpy(A,B,17)
#define   _IQ16mpy(A,B)  __IQmpy(A,B,16)
#define   _IQ15mpy(A,B)  __IQmpy(A,B,15)
#define   _IQ14mpy(A,B)  __IQmpy(A,B,14)
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
#define   _IQtoQ5(A)     (short) ((long)((A) * 32.0L))
#define   _IQtoQ4(A)     (short) ((long)((A) * 16.0L))
#define   _IQtoQ3(A)     (short) ((long)((A) * 8.0L))
#define   _IQtoQ2(A)     (short) ((long)((A) * 4.0L))
#define   _IQtoQ1(A)     (short) ((long)((A) * 2.0L))
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
