rbgusrns/JP_Robotrace/Software/main/menu.h

//###########################################################################
//
// FILE		: Menu.h
//
// TITLE	: Menu h file.
//
// Author	: Yuk Keun Ho
//
// Company	: MAZE
//
//###########################################################################
// $Release Date: 2011.11.16 $
//###########################################################################

#ifndef __MENU_H__
#define __MENU_H__


#define	Left_SW			(!(GpioDataRegs.GPBDAT.bit.GPIO33))
#define	Right_SW		(!(GpioDataRegs.GPBDAT.bit.GPIO34))
#define	Up_SW			(!(GpioDataRegs.GPADAT.bit.GPIO30))
#define	Down_SW			(!(GpioDataRegs.GPADAT.bit.GPIO31))

#define	Left_W			(g_lm.q17cur_vel_avr > _IQ(200))
#define	Right_W		    (g_lm.q17cur_vel_avr < _IQ(-200))
#define	Down_W			( (g_rm.q17cur_vel_avr < _IQ(-200)) || (g_rm.q17cur_vel_avr > _IQ(100)) )



#define ROW			4
#define	COLUMN		6
#define VFD_LIST	9

#define DELAY	135000 // 0.125sec

extern	void menu_start(void);
extern	void menu(void);

extern void vel_control(void);
extern void bril_run_start(void);
extern void fast_run(void);
extern void fst_info(void);
extern void bril_info(void);
extern void F_bril_select();





#endif
