rbgusrns/JP_Robotrace/Software/include/exception.h

/******************************************************************************
*                                                             \  ___  /       *
*                                                               /   \         *
* Edison Design Group C++  Runtime                           - | \^/ | -      *
* Copyright 1993-2004 Edison Design Group, Inc.                 \   /         *
* All rights reserved.  Consult your license regarding        /  | |  \       *
* permissions and restrictions.                                  [_]          *
*                                                                             *
******************************************************************************/
/*
The exception header should be included as "#include <exception>".
This file is provided for compatibility with older programs that
use "#include <exception.h>".
*/
#ifndef _EXCEPTION_H
#define _EXCEPTION_H

#include <exception>

#endif /* _EXCEPTION_H */

/******************************************************************************
*                                                             \  ___  /       *
*                                                               /   \         *
* Edison Design Group C++  Runtime                           - | \^/ | -      *
* Copyright 1993-2004 Edison Design Group, Inc.                 \   /         *
* All rights reserved.  Consult your license regarding        /  | |  \       *
* permissions and restrictions.                                  [_]          *
*                                                                             *
******************************************************************************/
