rbgusrns/JP_Robotrace/Software/include/iso646.h

/*****************************************************************************/
/* ISO646.H v4.1.3                                                           */
/* Copyright (c) 2000-2006 Texas Instruments Incorporated                    */
/*****************************************************************************/
#define and    &&
#define and_eq &=
#define bitand &
#define bitor  |
#define compl  ~
#define not    !
#define not_eq !=
#define or     ||
#define or_eq  |=
#define xor    ^
#define xor_eq ^=
